phelelep/ProjetElecLORA_GSM/CompteRendu_Xavier/08_10_2025.md

# CR - MIRRIONE Xavier  
## Séance du 08/10/2025  
Schéma général projet
---

### Compréhension du projet

Le projet consiste à rendre **connectée une ruche**.Elle sera capable de collecter et transmettre des données à distance via GSM, soit SMS Téléphone.  
Deux principaux sytèmes sont utilisés :
- **LoRa** : module permettant l’envoi de données avec une **très faible consommation d’énergie**, mais un **débit limité**. Il sert à **récupérer les informations** provenant de toutes les ruches.  
- **GSM (SIM7000G)** : module de communication **longue portée**, utilisé pour **transmettre les données** LoRa vers un **téléphone** ou un **serveur en ligne**.

L’ensemble du circuit est alimenté par une **source d’énergie externe de 3.5 V**.

**Exemples de données collectées :**
- Température de la ruche  
- Poids de la ruche

Schéma général projet

---

### Prise en main du projet précédent

- La carte électronique fabriquée par l’équipe précédente ne sera pas réutilisée, car elle n’est pas fonctionnelle.  
- Nous allons utiliser une breadboard pour réaliser les connexions entre les modules à l’aide de fils.  
  → Cela permettra de tester et valider chaque module séparément avant d’intégrer le tout sur un PCB final.  
- Une partie du code LoRa de l’équipe précédente est disponible dans leur compte rendu.  
- Nous allons nous baser sur leur travail pour avancer plus rapidement et efficacement dans notre propre développement.
- Le code pour la partie GSM étais fonctionnel 

---

### Prochaines étapes du projet

1. **Prendre en main la partie LoRa**
   - Vérifier le **bon fonctionnement du module LoRa**.  
   - Reprendre et tester le **code source** fourni par l’équipe précédente.  
   - S’assurer que la communication **en émission et réception** fonctionne correctement.
2. **Prise en main du Module GSM**
    - arriver à envoeyr des messages avec une carte SIM
3. **Rélier Lora en utilisant l'ESP32 pour établier une communication avec le GSM**  
    - Integration LoRA & ESP32
    - Ajout du GSM

**Outils utilisés :**
- Logiciel : **Arduino IDE**  
- Code source : celui de l'ancienne l’équipe va être réutilisé et amélioré si nécessaire en fonction de nos besoins.

---
