phelelep/ProjetElecLORA_GSM/eco_conception/Project eco-conception.docx

# Projet Eco conception

GATEWAY LORA-GSM

# Étape 1 — Contexte environnemental et enjeux du numérique

Le secteur numérique représente aujourd’hui environ 4 à 5 % des émissions mondiales de gaz à effet de serre, avec un taux de croissance rapide. Au-delà du carbone, les équipements électroniques (EEE) posent des problèmes spécifiques à chaque phase de leur vie.

Fabrication : utilisation de matériaux rares (déplétion des ressources abiotiques), émissions GES importantes (ex. STMicroelectronics à Rousset : > 300 GWh/an), consommation d’eau (1,5 million de m³/an à Rousset).

Usage : principalement de l’énergie électrique, mais multiplié par le nombre très élevé d’appareils en service.

Fin de vie : génère des déchets électroniques (e-waste) fortement polluants. En 2022, 62 millions de tonnes de déchets électroniques produits dans le monde, dont seulement 22,3 % collectés et recyclés (Global E-waste Monitor 2022).

Pour les ingénieurs, l’écoconception représente un levier majeur : réduire la taille des puces, utiliser moins de matériaux rares dès la phase de design, prévoir le démontage et le recyclage.

# Étape 2 — Qu’est-ce que l’ACV ?

“ L’ACV est une méthode permettant de mesurer les impacts environnementaux d’un produit ou d’un service. ” — Pr. Luc Deneire, Polytech Nice Sophia Antipolis

Elle couvre l’intégralité du cycle de vie du produit : de l’extraction des matières premières jusqu’à la fin de vie, en passant par la fabrication, la distribution et l’usage.

## ACV Attributionnelle

Décrit tous les flux physiques pertinents qui contribuent et qui sont la conséquence d’un cycle de vie.

- Objectif principal 1 : identifier quels sous-systèmes (composants) ont le plus d’impact.
- Objectif principal 2 : identifier quelles phases du cycle de vie (fabrication, usage, fin de vie) ont le plus d’impact.
- Approche retenue pour ce projet.

## ACV Conséquentielle

Décrit quels flux environnementaux seront le plus impactés par des modifications de conception du produit.

- Objectif principal : déterminer quelle modification du produit a du sens sur le plan environnemental.
- Sera utilisée en phase d’interprétation pour formuler des recommandations.

# Étape 3 — Portées de l’ACV

Trois périmètres sont possibles selon la norme ISO 14040 :

Cradle to grave (Berceau à tombe) : périmètre le plus complet — de l’extraction des matières premières jusqu’à la fin de vie (recyclage ou mise en décharge). C’est le périmètre retenu pour ce projet.

Cradle to gate (Berceau à porte) : de l’extraction jusqu’à la sortie d’usine. Adapté quand la phase usage est negligeable ou inconnue.

Gate to gate (Porte à porte) : uniquement la phase de fabrication. Utile pour comparer deux procédés de production.

Choix pour ce projet : Cradle to grave — nous intégrons la fabrication, 5 ans d’usage (électricité de recharge) et la fin de vie (collecte DEEE).

# Étape 4 — Définition et objectifs de l’ACV

## Objectifs

Cette ACV attributionnelle a pour but d’évaluer l’empreinte environnementale de la passerelle LoRa-GSM conçue dans le cadre du projet ruche connectée. Elle est réalisée dans un contexte académique (cours d’écoconception, Polytech, Université Côte d’Azur). Le produit étudié est un prototype.

## Unité fonctionnelle (UF)

Selon le cours (slide 30), l’unité fonctionnelle doit suivre le format : verbe d’action + niveau de performance quantifié + conditions d’utilisation.

“ Assurer la collecte locale (via LoRa) et la transmission distante (via GSM/LTE) des paramètres environnementaux d’une ruche, à une fréquence d’un envoi toutes les heures, dans un environnement rural extérieur (IP65), pour une durée de vie anticipée de 5 ans. ”

Questions soulevées par la durée de vie (analogie avec l’exemple du convertisseur Buck du cours) :

- La durée de vie réelle de la batterie LiPo est-elle de 5 ans ? Un remplacement anticipé (2–3 ans) multiplierait l’impact de ce composant.
- Où fonctionne la gateway ? En France, le mix électrique est bas-carbone (0,057 kg CO₂eq/kWh). Dans un pays au mix charbon, l’impact de la phase usage serait nettement plus élevé.
- Le mode Deep Sleep de l’ESP32 et du module LoRa est activement utilisé, ce qui réduit significativement la consommation en phase usage.

## Champ de l’étude (Scope)

Périmètre : Cradle to grave — extraction des matières premières → fabrication → usage 5 ans → fin de vie.

## Flot de référence

Quantité du produit nécessaire pour atteindre l’unité fonctionnelle : 1 unité de passerelle LoRa-GSM (masse totale ≈ 276 g, hors énergie).

## Frontières du système

Inclus : extraction des matières premières, fabrication des composants électroniques (ESP32, SIM7000G, LLCC68, PCB, passifs), assemblage, phase d’usage 5 ans (électricité de recharge batterie : 87,6 kWh), fin de vie DEEE.

Exclus : phase R&D, transport entre usines, infrastructure serveur de réception des données, maintenance et remplacement de composants hors batterie.

Localisation : usage en France — mix électrique français, source Electricity Maps.

Période : 5 ans de fonctionnement.

# Étape 5 — Inventaire — Bill of Materials (BOM)

Pour l’électronique, l’inventaire du cycle de vie repose principalement sur le BOM (Bill of Materials), comme indiqué en slide 33 du cours. Le tableau ci-dessous liste l’ensemble des composants de la passerelle LoRa-GSM avec leur correspondance dans la base de données EcoInvent, tels qu’ils ont été introduits dans le logiciel OpenLCA.

Bloc / Module | Désignation | Nom EcoInvent | Cat. | Qté | Masse/Surface | Unité
ESP32 WROOM | Circuit imprimé (PCB) | printed wiring board, SMT, Pb-free | PCB | 1 | 0,0072 m² | m²
ESP32 WROOM | Montage CMS PCB | mounting, SMT, Pb-free solder | PCB | 1 | 0,0072 m² | m²
ESP32 WROOM | Microcontrôleur ESP32 (QFN-40) | wafer, fabricated, for IC | IC | 1 | 25 mm² | mm²
ESP32 WROOM | Mémoire Flash SPI (SOIC-8) | integrated circuit, logic type | IC | 1 | 1,08 g | g
ESP32 WROOM | Oscillateur Quartz | integrated circuit, logic type | IC | 1 | 0,6 g | g
ESP32 WROOM | Condensateurs de découplage (0402) | capacitor, for SMT | Passif | 15 | 0,37 g/pèce | g
ESP32 WROOM | Résistances pull-up/down (0402) | resistor, surface-mounted | Passif | 10 | 0,10 g/pèce | g
SIM7000G | Circuit imprimé (PCB) | printed wiring board, SMT, Pb-free | PCB | 1 | 0,0072 m² | m²
SIM7000G | Montage CMS PCB | mounting, SMT, Pb-free solder | PCB | 1 | 0,0072 m² | m²
SIM7000G | Modem cellulaire (TFBGA-361) | wafer, fabricated, for IC | IC | 1 | 144 mm² | mm²
SIM7000G | Connecteurs antenne U.FL/SMA | electric connector, PCI buss | Périph. | 2 | 0,57 g/pèce | g
SIM7000G | Condensateurs tantale (1206) | capacitor, tantalum, through-hole | Passif | 4 | 0,016 g/pèce | g
SIM7000G | Support carte SIM | electric connector, peripheral | Périph. | 1 | 1,00 g | g
SIM7000G | Diodes de protection ESD (SOT-23) | integrated circuit, logic type | IC | 2 | 0,017 g/pèce | g
SIM7000G | Régulateur LDO (transistor SMD) | transistor, surface-mounted | Passif | 1 | 0,06 g | g
SIM7000G | Self DC/DC (inductance 1008) | inductor, low value multilayer chip | Passif | 1 | 0,112 g | g
LoRa LLCC68 | Circuit imprimé (PCB) | printed wiring board, SMT, Pb-free | PCB | 1 | 0,0072 m² | m²
LoRa LLCC68 | Montage CMS PCB | mounting, SMT, Pb-free solder | PCB | 1 | 0,0072 m² | m²
LoRa LLCC68 | Transceiver LoRa LLCC68 (QFN-24) | wafer, fabricated, for IC | IC | 1 | 16 mm² | mm²
LoRa LLCC68 | Oscillateur Quartz | integrated circuit, logic type | IC | 1 | 0,6 g | g
LoRa LLCC68 | Pin headers de connexion | electric connector, PCI buss | Périph. | 8 | 0,71 g/pèce | g
LoRa LLCC68 | Inductances RF d’adaptation (0402) | inductor, low value multilayer chip | Passif | 4 | 0,001 g/pèce | g
Cartes | Connecteur USB-C alimentation | electric connector, peripheral | Périph. | 1 | 2,25 g | g
Cartes | Boutons poussoir Reset/Boot | switch, toggle type | Passif | 2 | 4,00 g/pèce | g
Cartes | LEDs d’indicateur d’état (0603) | diode, glass, for SMT | Passif | 3 | 0,08 g/pèce | g
Cartes | Résistances pour LEDs (0603) | resistor, surface-mounted | Passif | 3 | 0,042 g/pèce | g
Batterie | Batterie Lithium-ion | battery, Li-ion — EcoInvent | Batterie | 1 | 20 g | g
Boîtier | Boîtier ABS IP65 | ABS plastic — EcoInvent | Boîtier | 1 | 150 g | g
Antennes | Antennes GSM + LoRa | — | — | 1 | 30 g | g
Énergie | Électricité usage (5 ans, France) | electricity, low voltage, FR | Énergie | 1 | 87,6 kWh | kWh
TOTAL | 30 références composants + énergie | | | | ≈ 276 g + 87,6 kWh

Le détail complet des correspondances EcoInvent est disponible dans le fichier composants_ecoinvent.xlsx joint au dépôt GitHub.

# Creation du processus et du flow

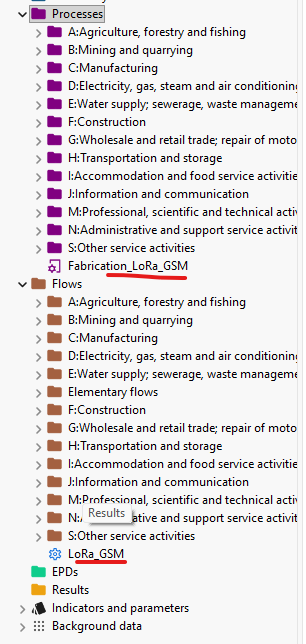
[picture p59: figure]

# Creation des inputs

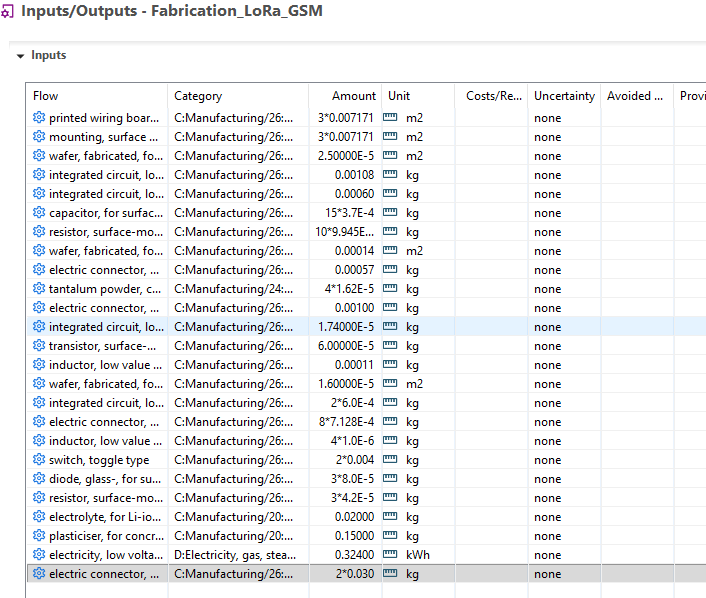
[picture p60: figure]

Les inputs dans le processus “Fabrication_ LoRa_GSM”

Chaquet donne du tableau Excel et été introduite

# Création du Product System

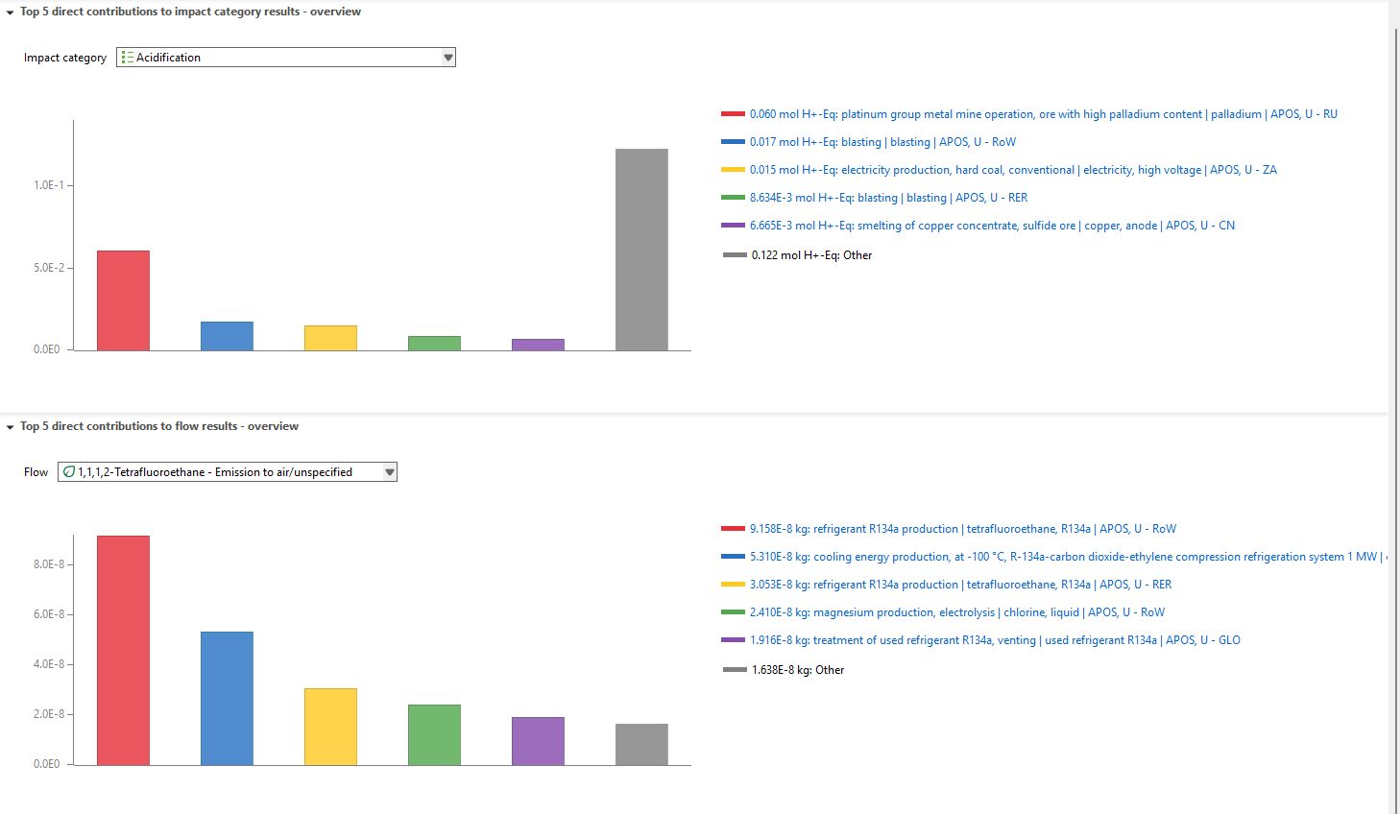
[picture p61: figure]
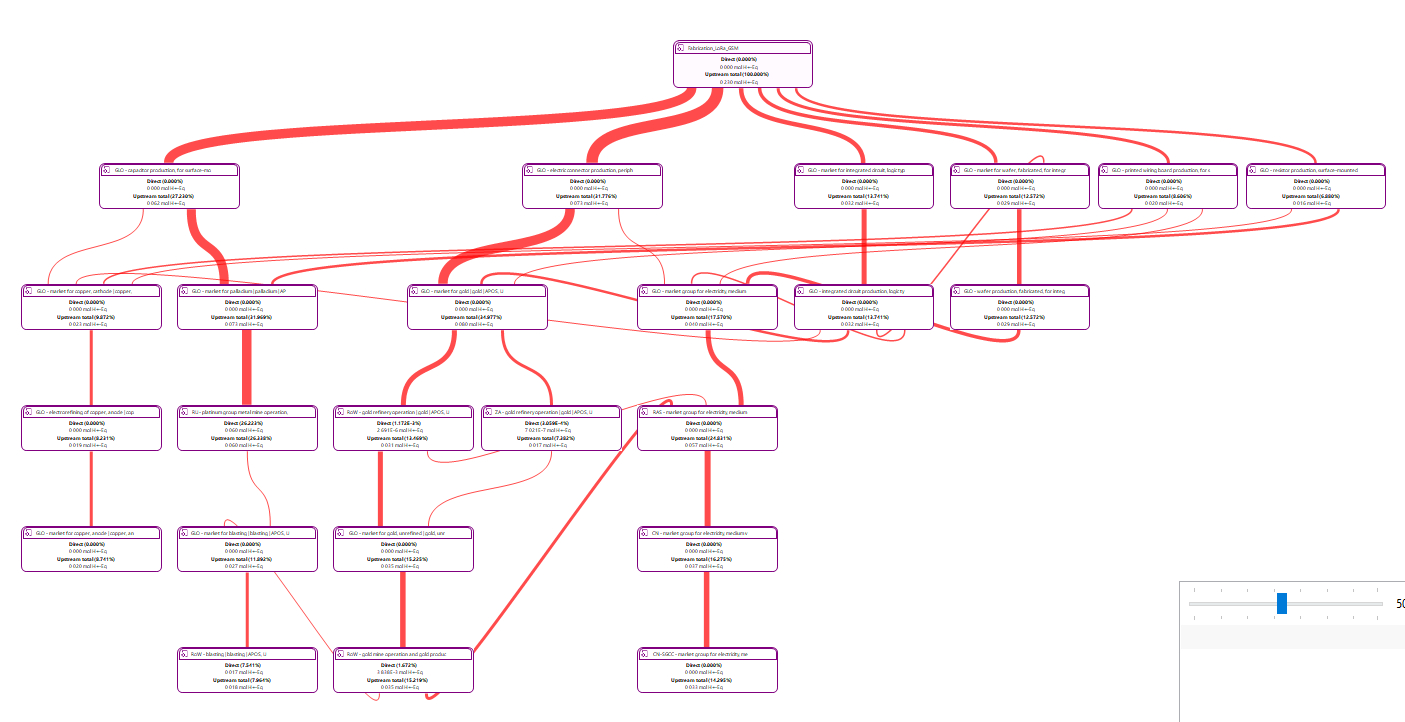
[picture p62: figure]

- On remarque que la fabrication La fabrication = 80-90% de l'impact
- L'usage (10-20% de l'impact) : Grâce à au LoRa et du Deep Sleep, la part de l'électricité sera très faible.

# Étape 7 — Analyse Opex vs Capex : fabrication vs usage

L’un des enseignements majeurs du cours (slides 17–18, illustré sur le smartphone) est le rapport entre l’impact à la fabrication (Capex) et l’impact à l’usage (Opex).

Capex (fabrication) : 80 à 90 % de l’impact total pour les équipements électroniques. Inclut l’extraction des matériaux rares, la production des semi-conducteurs et l’assemblage des cartes.

Opex (usage) : 10 à 20 % de l’impact. Principalement lié à la consommation électrique de recharge de la batterie.

Pour notre gateway, ce ratio est particulièrement favorable à la phase usage grâce aux deux optimisations logicielles clés implémentées dans le projet :

- Mode Deep Sleep de l’ESP32 : consommation descendant à quelques µA lors des périodes d’inactivité.
- Protocole LoRa : radio longue portée à très faible puissance (quelques mW en émission), contrairement au WiFi ou au Bluetooth classique.

La consommation estimée sur 5 ans est d’environ 87,6 kWh, soit environ 1,5 à 2 mAh par heure en moyenne. Avec le mix électrique français (0,057 kg CO₂eq/kWh), cela représente environ 5 kg CO₂eq sur 5 ans pour la seule phase usage, soit une fraction minoritaire du bilan total.

# L’analyse de l’impact de notre projet

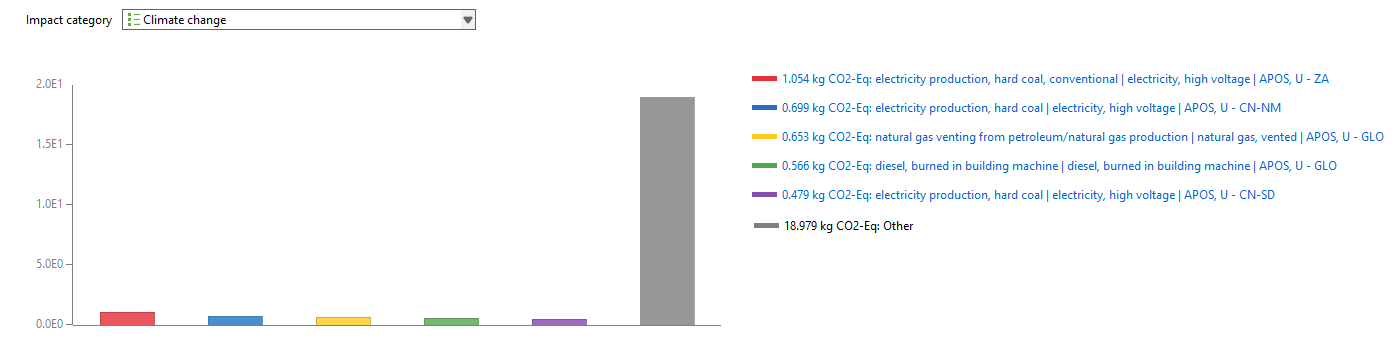
[picture p63: figure]

Notre Gateway de ruche émet environ 20 5 kg de CO2 sur l'ensemble de son cycle de vie (fabrication + 5 ans d'usage). Pour te donner une idée, c'est l'équivalent d'environ 100 à 120 km parcourus par une voiture thermique moyenne. Pour un objet électronique complexe (GSM + LoRa + Batterie), c'est un score très correct.

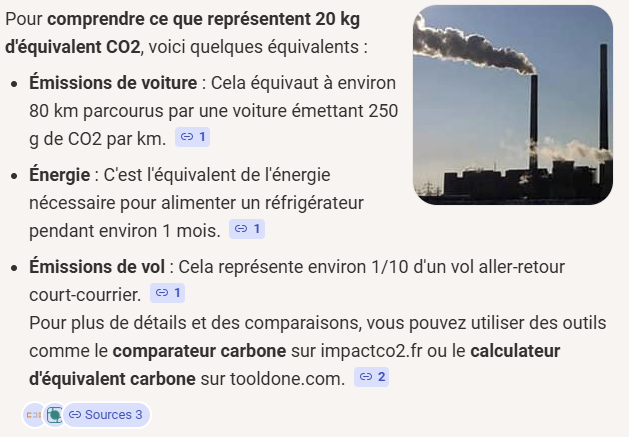
[picture p64: figure]

Source google.com

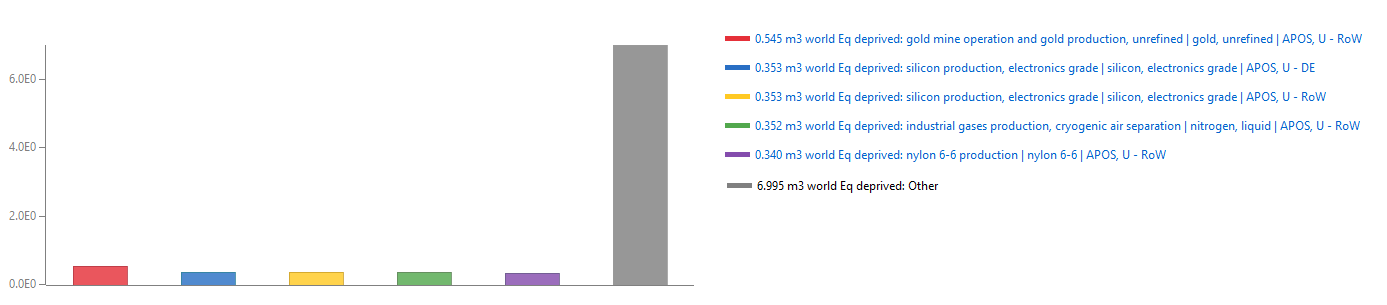
[picture p65: figure]

8m³ d'eau environ pour notre projet ce qui reste corect si le projet reste fonctionnel pendant 5 ans. Et condition qu’il ne nécessite pas une intervention humaine durant les 5 années.

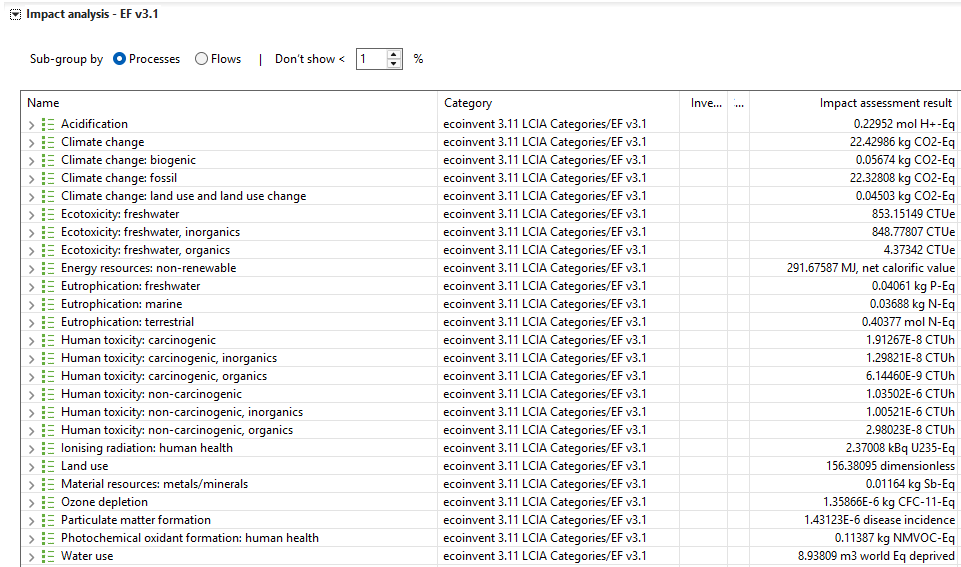
[picture p66: figure]

- Mineral resource scarcity : Ce chiffre représente l'épuisement des métaux (Or, Cuivre, Lithium). C'est souvent l'impact le plus fort de l'électronique.
- Terrestrial ecotoxicity : les ruches sont dans la nature. Cela mesure l'impact potentiel des composants si le boîtier se dégrade ou est mal recyclé.

# Étape 6 — Évaluation des impacts

## Les 16 catégories d’impact (méthode ReCiPe / CML)

La méthode ACV normalisée définit jusqu’à 16 catégories d’impact. Les résultats sont exprimés en unités communes (impacts mid-point), puis peuvent être agrégés en impacts end-point sur la santé, les écosystèmes et les ressources.

# | Catégorie d’impact | Unité | Priorité | Pertinence pour l’électronique

1 | Climate change | kg CO₂ eq | ★★★ | Principale — émissions GES de la fabrication et de l’usage
2 | Mineral resource scarcity | kg Cu eq | ★★★ | Principale — métaux rares : or, cuivre, lithium, cobalt
3 | Water consumption | m³ eq | ★★★ | Principale — semi-conducteurs très consommateurs en eau
4 | Terrestrial ecotoxicity | kg 1,4-DCB | ★★★ | Principale — dégradation boîtier ou mauvais recyclage DEEE
5 | Human toxicity (cancer) | kg 1,4-DCB | ★★★ | Principale — traitement des semi-conducteurs
6 | Ozone depletion | kg CFC-11 eq | ★
7 | Ionizing radiation | kBq Co-60 eq | ★
8 | Photochemical ozone formation | kg NMVOCs | ★★
9 | Particulate matter formation | kg PM₂,5 eq | ★★
10 | Terrestrial acidification | kg SO₂ eq | ★★
11 | Freshwater eutrophication | kg P eq | ★
12 | Marine eutrophication | kg N eq | ★
13 | Freshwater ecotoxicity | kg 1,4-DCB | ★★
14 | Marine ecotoxicity | kg 1,4-DCB | ★★
15 | Land use | m² annum crop eq | ★
16 | Fossil resource scarcity | kg oil eq | ★★

Légende : ★★★ = catégorie principale pour l’électronique (mise en évidence en jaune), ★★ = catégorie secondaire, ★ = faible pertinence pour ce type de produit.

## Résultats obtenus sur OpenLCA pour notre passerelle

# L’analyse de la contribution

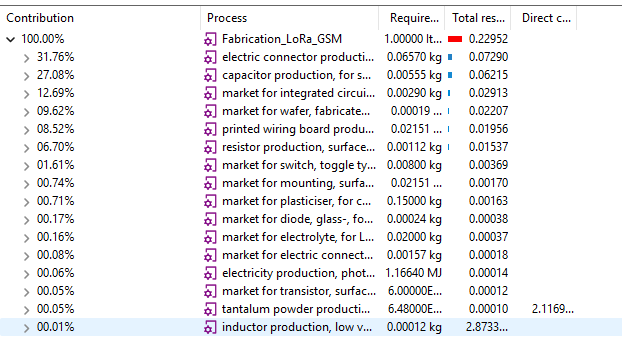
[picture p67: figure]

D'après le graphique c’est l'extraction des matériaux et la fabrication des composants complexes (puces, PCB) qui pèsent le plus.

# Étape 8 — Interprétation des résultats

## Principaux enseignements de l’ACV

Les résultats obtenus dans OpenLCA confirment le schéma classique de l’électronique : la fabrication représente 80–90 % de l’impact total. Ce ratio est identique à celui du smartphone présenté en cours (slides 22–24).

Climate change (≈ 20,5 kg CO₂eq) : Équivalent à 100–120 km en voiture thermique. Pour un objet combinant GSM + LoRa + batterie, c’est un bilan très correct.

Water consumption (≈ 8 m³) : Essentiellement lié à la fabrication des semi-conducteurs (silicium, cuivre). Acceptable sur 5 ans sans intervention.

Mineral resource scarcity : L’impact le plus élevé proportionnellement — extraction d’or, cuivre, lithium, cobalt. Surtout dô à la batterie LiPo et aux PCB multicouches.

Terrestrial ecotoxicity : Indicateur à surveiller car les ruches sont en milieu naturel. L’impact survient si le boîtier se dégrade ou si le produit est mal recyclé (DEEE).

L’analyse de contribution confirme que les composants complexes (puces électroniques, PCB multicouches) et l’extraction des métaux constituent les “points chauds” prioritaires sur lesquels concentrer les efforts d’amélioration.

## Recommandations d’écoconception (ACV conséquentielle)

Sur la base de l’ACV attributionnelle, les pistes d’amélioration suivantes sont identifiées (approche conséquentielle, slide 21) :

1. Prolonger la durée de vie : Passer de 5 à 10 ans diviserait l’impact fabrication par deux sur l’unité fonctionnelle. Cela implique de choisir des composants à MTBF élevé et de prévoir des mises à jour logicielles (firmware OTA).

2. Réduire la capacité de la batterie : Le Deep Sleep permet d’évaluer si une batterie plus petite (1 000 mAh) suffit, réduisant l’impact du lithium et du cobalt.

3. Faciliter le démontage et le recyclage : Utiliser des vis plutôt que de la colle, marquer clairement les plastiques (ABS), prévoir la séparabilité batterie/PCB pour le tri DEEE.

4. Optimiser le PCB : Un PCB 2 couches au lieu de 4 réduit la quantité de cuivre et de résine époxy ; envisager un PCB sans halogène (halogen-free) pour limiter l’écotoxicité.

5. Localisation de la fabrication : Assembler en Europe avec de l’électricité renouvelable réduit les émissions de fabrication.

# Étape 9 — Comparaison avec l’exemple du cours (convertisseur Buck)

Le professeur utilise en cours (slides 37–38) un convertisseur Buck disponible sur GitHub comme exemple pratique d’ACV. La comparaison avec notre gateway est instructive :

Unité fonctionnelle du Buck (cours) : “ Assurer la régulation d’une tension continue (abaissement de 12 V à 5 V) pour une charge de 5 W pendant 15 000 heures de fonctionnement. ”

Unité fonctionnelle de notre gateway : “ Assurer la collecte et la transmission des données environnementales d’une ruche via LoRa et GSM/LTE, pendant 5 ans de fonctionnement extérieur. ”

Les mêmes questions que le prof pose pour le Buck s’appliquent à notre projet :

- La batterie est-elle bien dimensionnée pour 5 ans ? Si la durée de vie réelle est de 2–3 ans, l’impact de ce composant doit être multiplié.
- Le circuit est-il bien dimensionné pour la charge réelle ? Le mode Deep Sleep réduit fortement la consommation effective.
- Où fonctionne le circuit ? Le mix électrique français est favorable (nucléaire + renouvelables = 0,057 kg CO₂eq/kWh vs > 0,4 en Pologne ou Allemagne).

# Étape 10 — Vocabulaire OpenLCA

Après démarrage d’OpenLCA et chargement de la base EcoInvent, les concepts clés utilisés dans ce projet sont les suivants :

Process : Le processus de fabrication ou d’usage. Dans notre cas : “ Fabrication_LoRa_GSM ” (regroup e tous les composants du BOM) et “ Usage_LoRa_GSM ” (87,6 kWh d’électricité sur 5 ans).

Flow : Les flux entrants (inputs : matériaux, énergie) et sortants (outputs : produit fini, déchets). Chaque ligne du BOM correspond à un flow entrant dans le processus de fabrication.

Product System : L’assemblage de tous les processus liés au cycle de vie. Il connecte fabrication, usage et fin de vie en un seul système à évaluer.

Impact Assessment : Le calcul des indicateurs environnementaux à partir des flux physiques. OpenLCA utilise les données EcoInvent pour convertir les masses de composants en kg CO₂eq, m³ d’eau, etc.

Reference Flow : La quantité de référence du produit à évaluer. Ici : 1 unité de gateway LoRa-GSM.

Annexe :

## Sources utilises :

Composant | Information à extraire | Source
ESP32 WROOM | Consommation | ESP32 Wi-Fi & Bluetooth Modules I Espressif (https://www.espressif.com/en/products/modules/esp32)
SIM7000G | Courant de transmission LTE | https://www.simcom.com/product/SIM7000G.html - Recherche Google (https://www.google.com/search?q=https://www.simcom.com/product/SIM7000G.html)
Poids des CMS | Masse des résistances/condos | mouser.fr
Boitier ABS | Masse et Volume plastique | https://www.hammondmfg.com/scpg.htm - Recherche Google (https://www.google.com/search?q=https://www.hammondmfg.com/scpg.htm)
Facteurs d'impact | Emissions CO2 des matériaux | Base Empreinte® (https://base-empreinte.ademe.fr/)
Mix Électrique | Impact du kWh par pays | Carte | Electricity Maps (https://app.electricitymaps.com/map/live/fifteen_minutes)

CEBAN Daniel & MIRRIONE Xavier

Éco conception 2025-2026 CEBAN Daniel & MIRRIONE Xavier _________________________________________________________________________________
