phelelep/ProjetElecLORA_GSM/Presentation finale projetLoRa-GSM.pdf

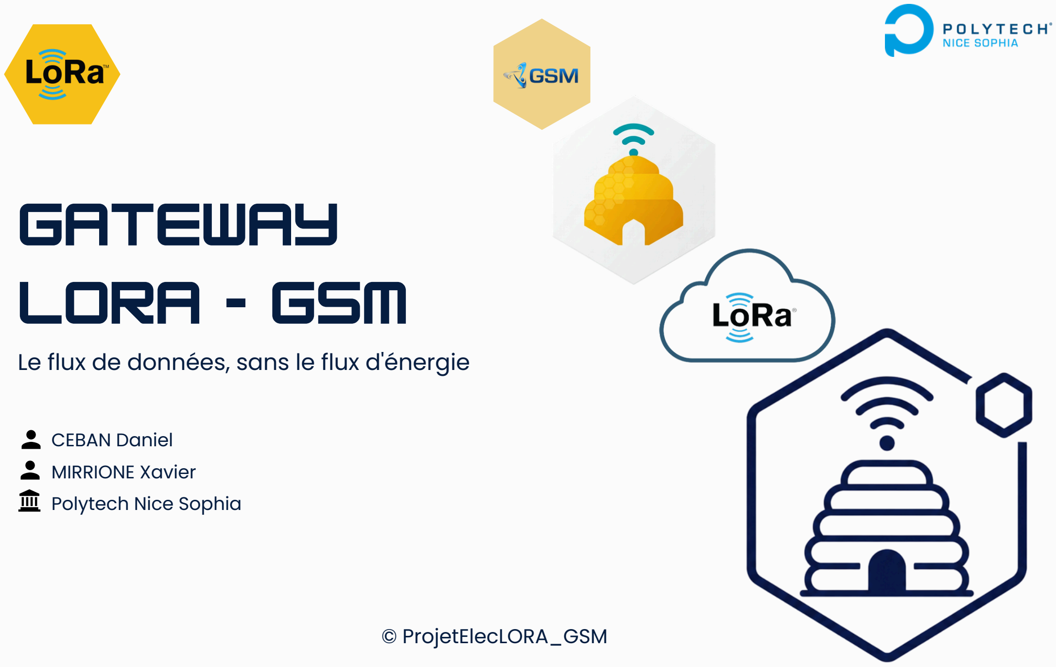
[picture p68: page 1]

Le flux de données, sans le flux d'énergie

# GATEWAY LORA - GSM

© ProjetElecLORA_GSM

CEBAN Daniel
MIRRIONE Xavier
Polytech Nice Sophia

# SOMMAIRE

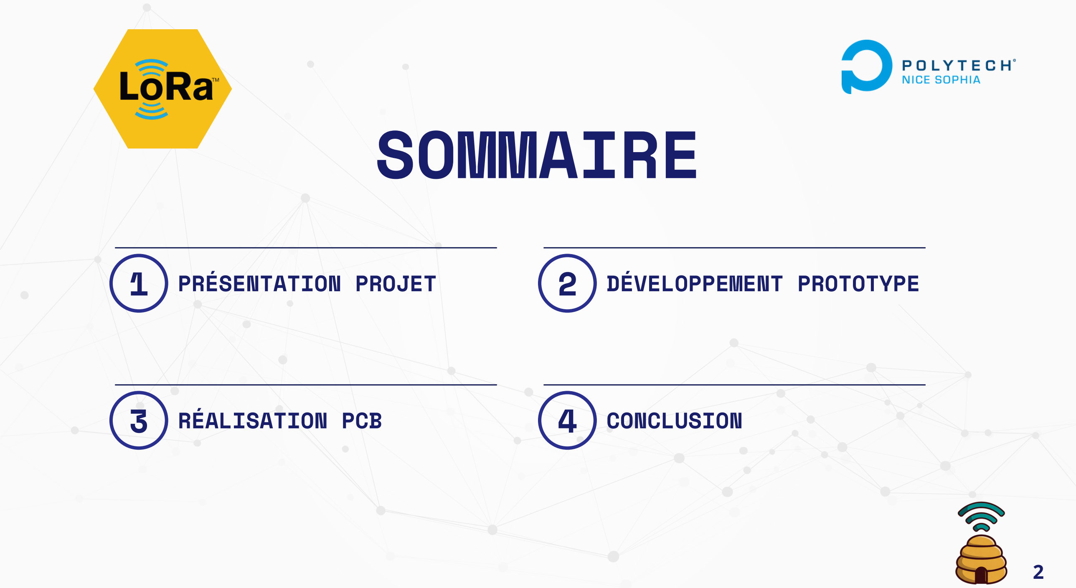
[picture p69: page 2]

1 PRÉSENTATION PROJET | 2 DÉVELOPPEMENT PROTOTYPE
3 RÉALISATION PCB | 4 CONCLUSION

2

# PRÉSENTATION PROJET

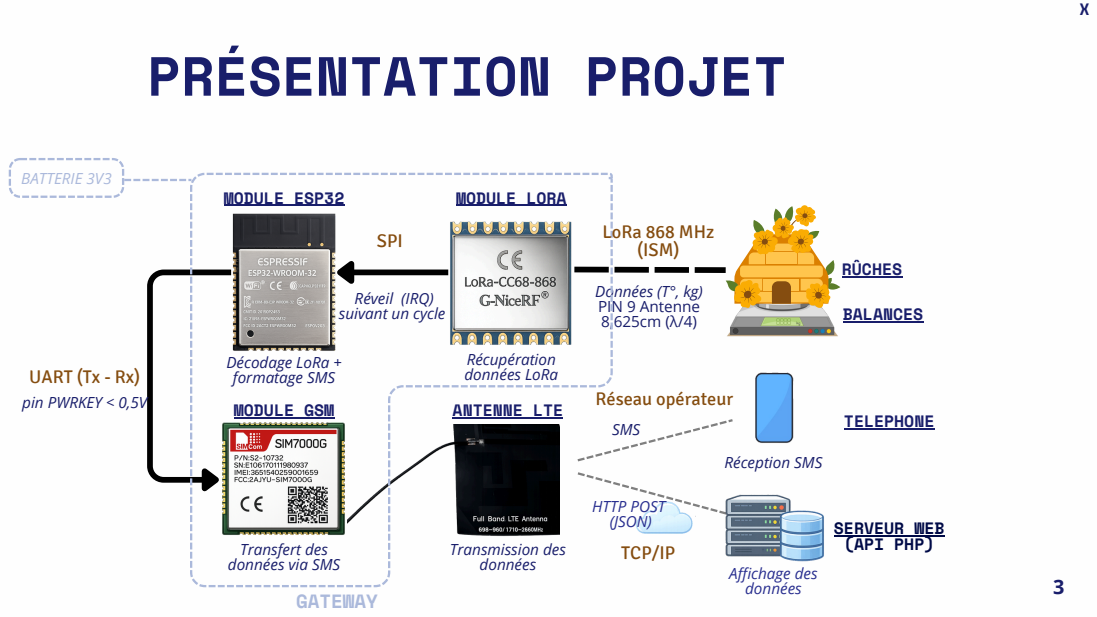
[picture p70: page 3]
Décodage LoRa + formatage SMS; Données (T°; , kg) PIN 9 Antenne 8,625cm (λ/4); SPI; Récupération données LoRa; MODULE ESP32; MODULE LORA; MODULE GSM; Transmission des données; ANTENNE LTE; Réseau opérateur; SMS; BATTERIE 3V3; Réception SMS; TELEPHONE; RÛCHES; BALANCES; LoRa 868 MHz (ISM); SERVEUR WEB (API PHP); Affichage des données; TCP/IP; HTTP POST (JSON)

Réveil (IRQ)
suivant un cycle

UART (Tx - Rx)
pin PWRKEY < 0,5V

Transfert des
données via SMS
GATEWAY

## AGENCEMENT DU TRAVAIL D’ÉQUIPE

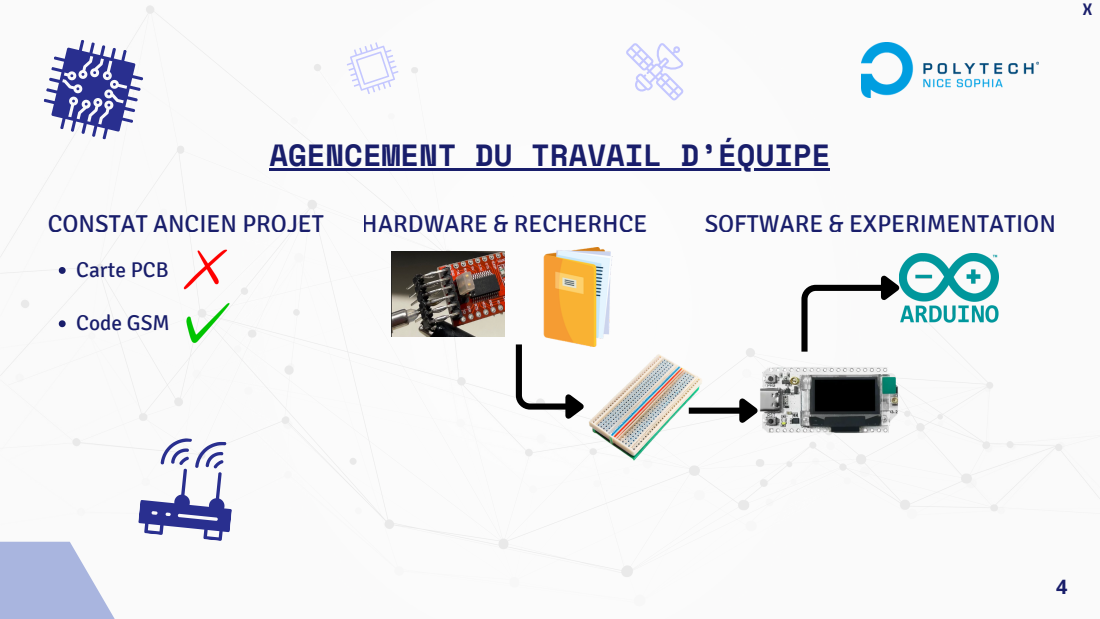
[picture p71: page 4]
CONSTAT ANCIEN PROJET; HARDWARE & RECHERHCE; SOFTWARE & EXPERIMENTATION; Carte PCB; Code GSM

# Développement prototype

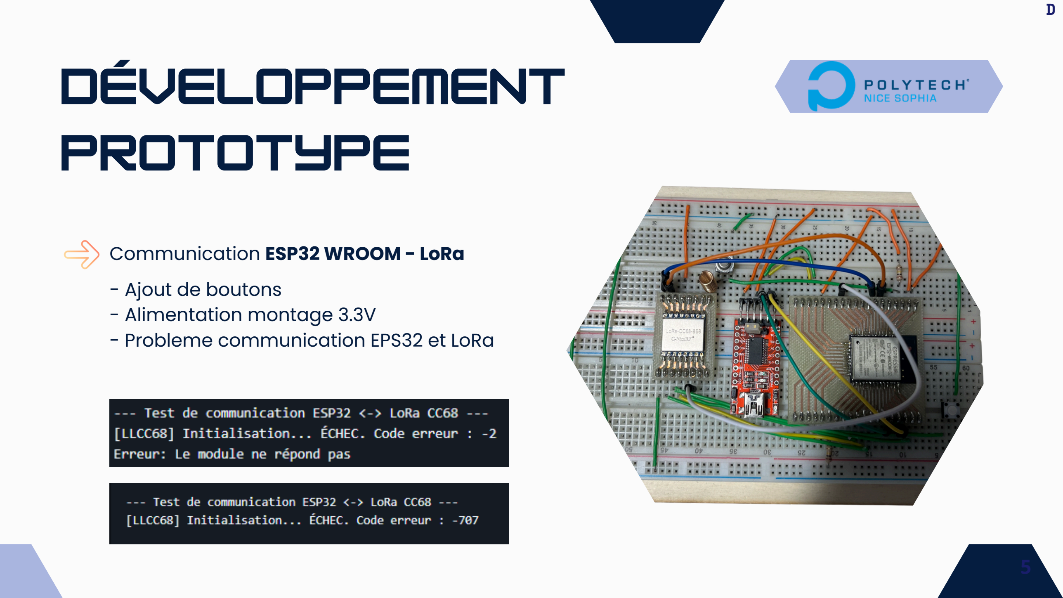
[picture p72: page 5]

5

Communication ESP32 WROOM - LoRa
- Ajout de boutons
- Alimentation montage 3.3V
- Probleme communication EPS32 et LoRa

D

# Développement prototype

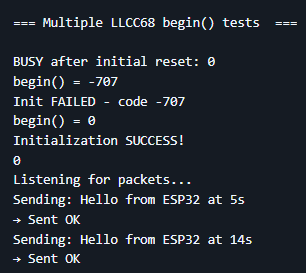
[picture p73: figure]

- Tests avec la bibliothèque “LoRa.h” et “RadioLib.h”

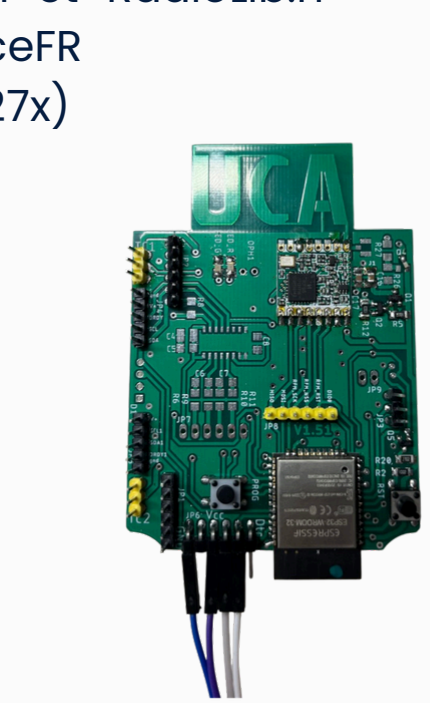
[picture p74: figure]

- Tests avec LoRa-CC68-868 G-NiceFR
- Test avec module RF96 (type SX127x)
- Tests en boucle

RÉSOLUTION PROBLÈME COMMUNICATION

6

# Développement prototype

7

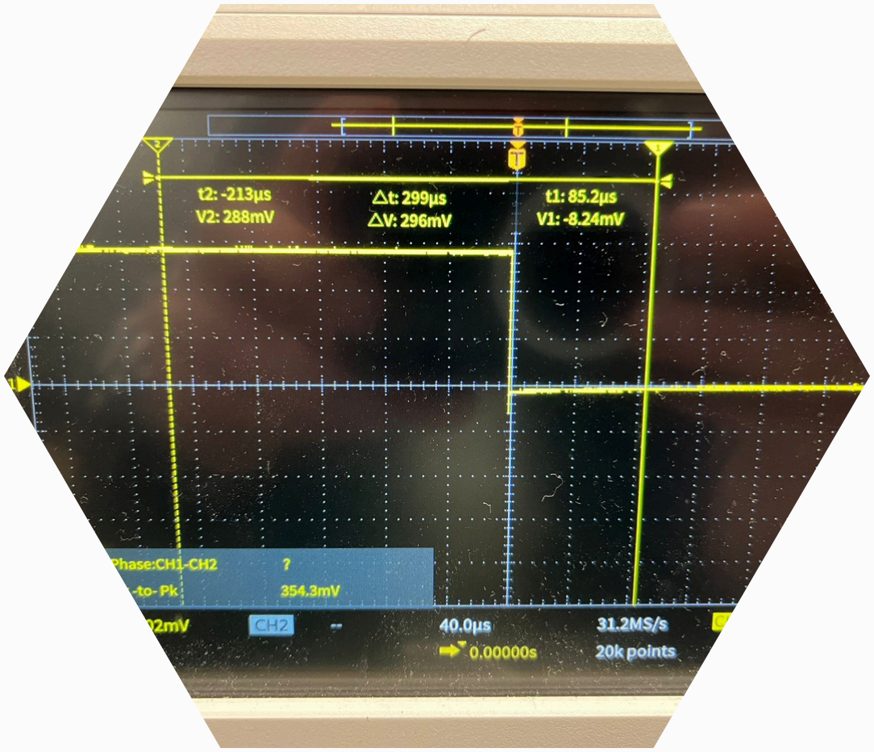
[picture p75: figure]

Réveil de l’ESP32 par LoRa
-LoRa : écouté en permanence -LoRa : Impulsion sur le pin DIO1 si message reçu
-ESP32 : réveil si impulsion du pin DIO1 -ESP32 : réinitialiser le DIO1 à “LOW” -ESP32 : réceptionner et traitement du message
-ESP32 : endormissement après 10 secondes d’inactivité

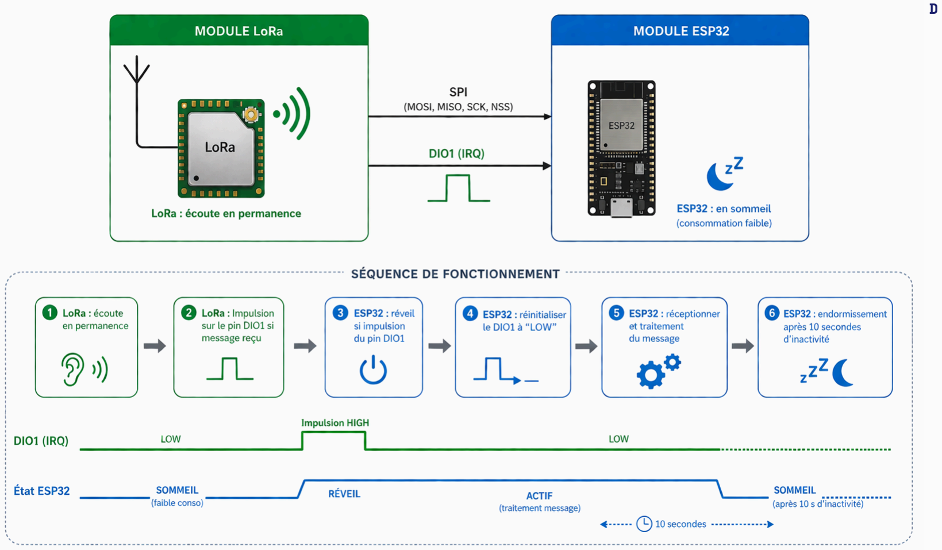
[picture p76: page 8]

# Développement prototype

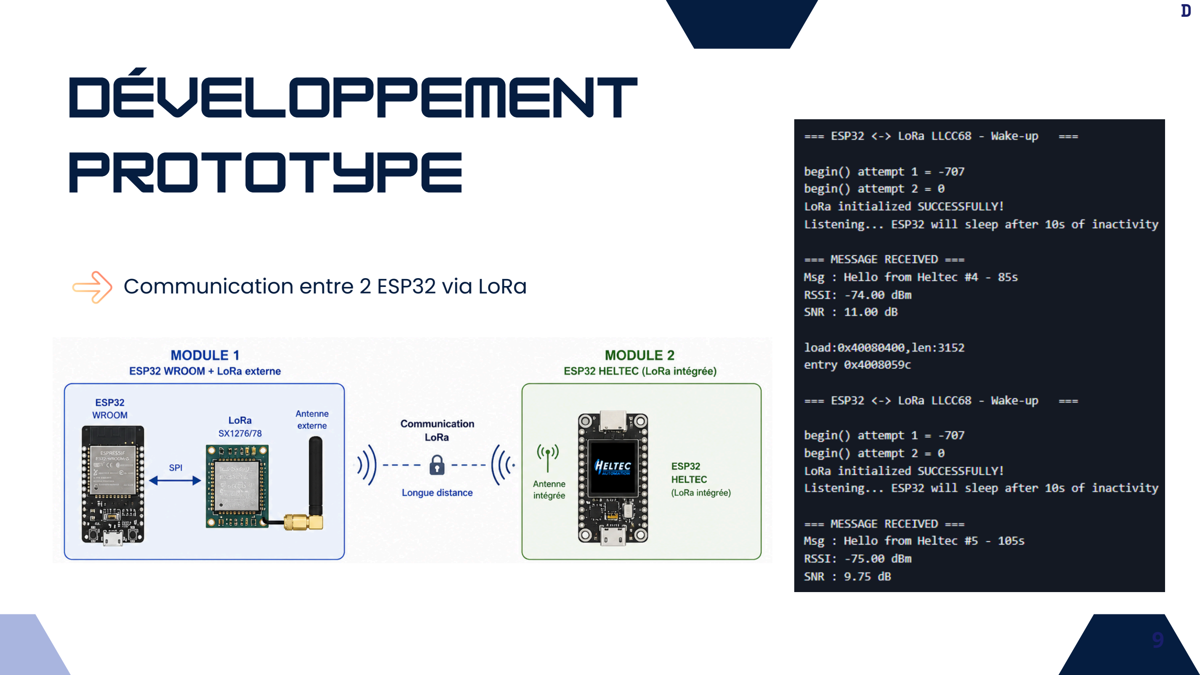
[picture p77: page 9]

9

Communication entre 2 ESP32 via LoRa

# Développement prototype

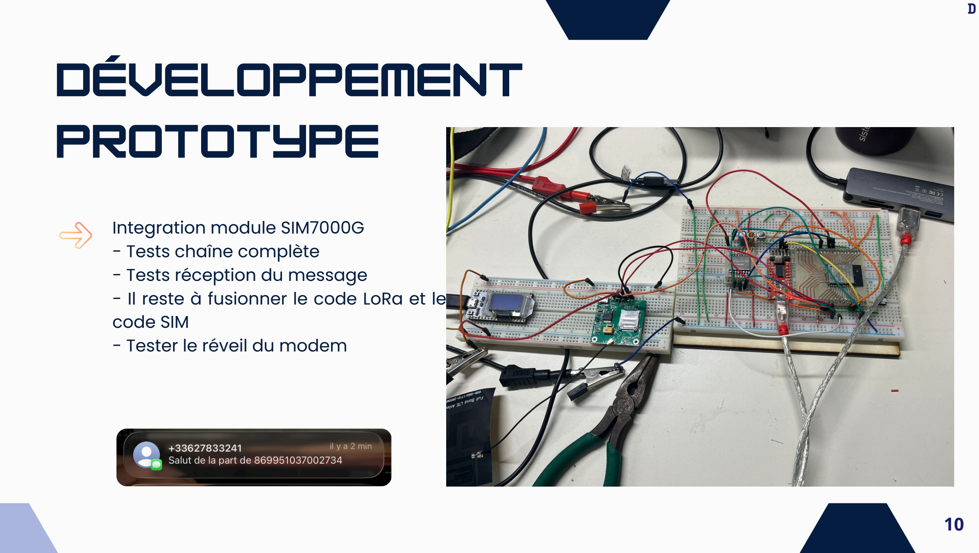
[picture p78: page 10]

10

Integration module SIM7000G
- Tests chaîne complète
- Tests réception du message
- Il reste à fusionner le code LoRa et le code SIM
- Tester le réveil du modem

# Réalisation PCB

11

X

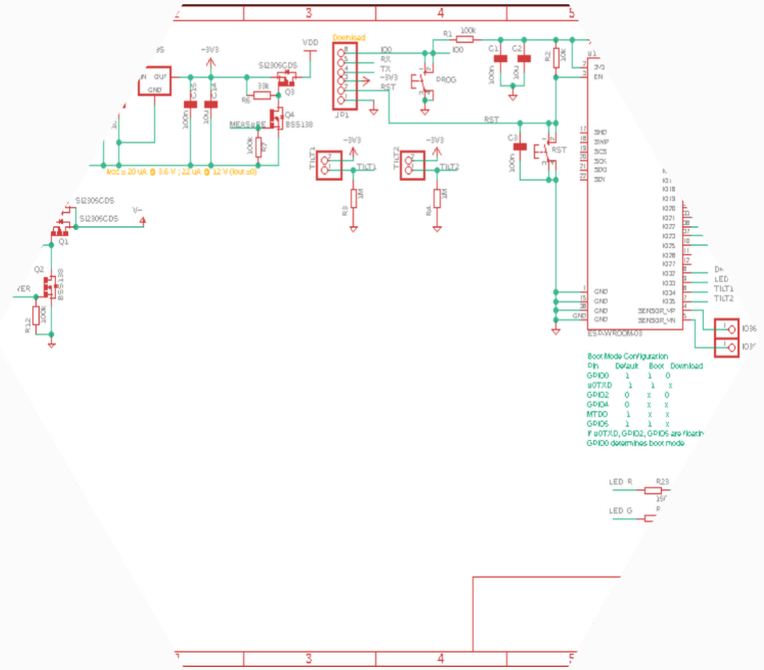
[picture p79: figure]

Réfléchir fonctionnellement, sans contraintes physiques Étapes clés de la réalisation :
1. Choix des composants et connexions (datasheets)
2. Composants passifs : condensateurs & résistances
3. Boutons RST & PROG pour la programmation
4. Circuit commande alimentation
Point de départ : version de l'

ancien groupe (ESP32 +
LoRa intégré)

# Réalisation PCB

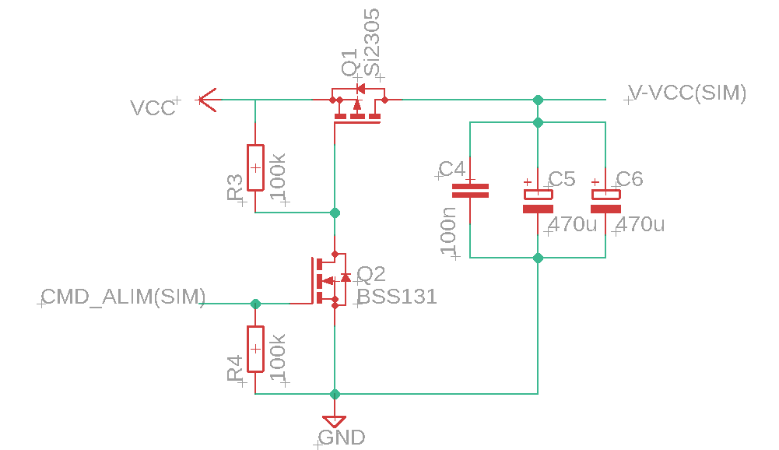
[picture p80: figure]

12

X

Problème : SIM7000G en mode sleep = 1,2 mA
Exigence prof : courant = 0 quand le module est inutilisé
Solution : coupure hardware via 2 transistors MOSFET
NMOS : BSS 131 & PMOS : SI2305 Contrôle : GPIO ESP32 (CMD_ALIM) coupe complètement l'

alimentation
SIM7000G

# Réalisation PCB

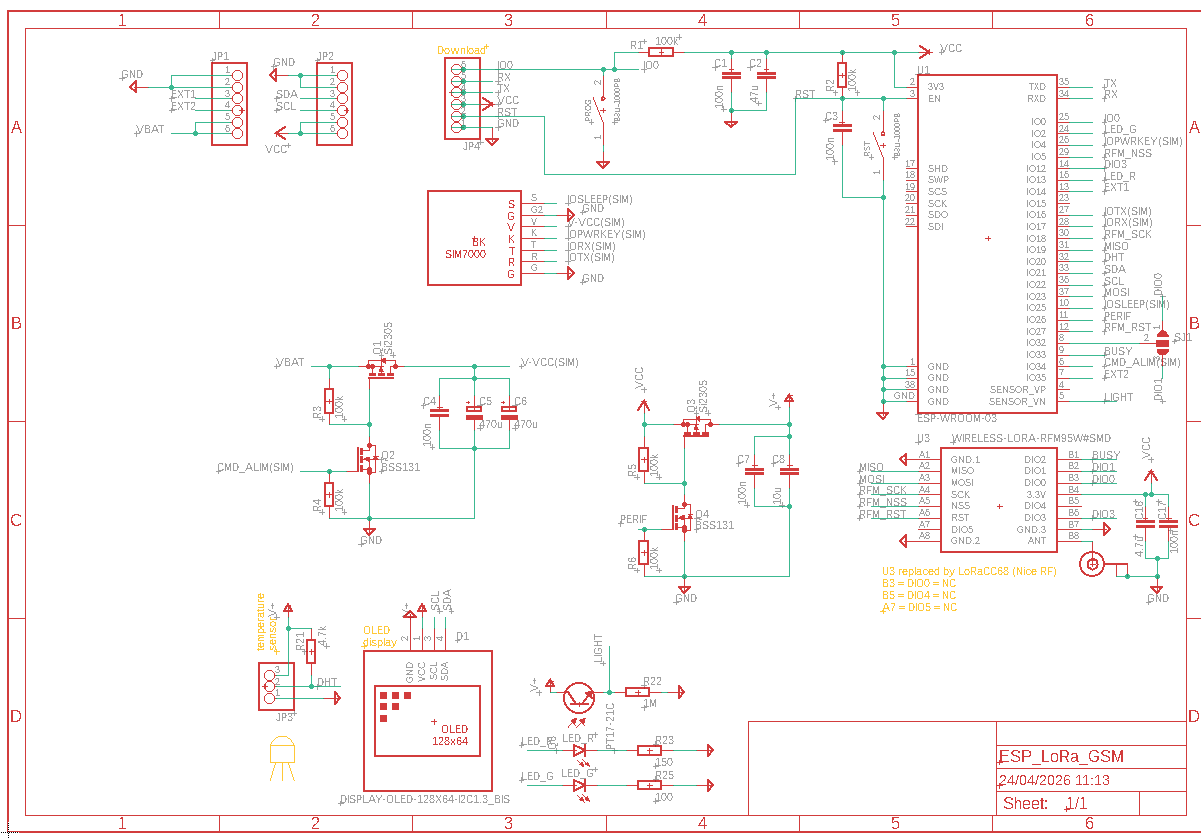
[picture p81: figure]

13

X

# Réalisation PCB

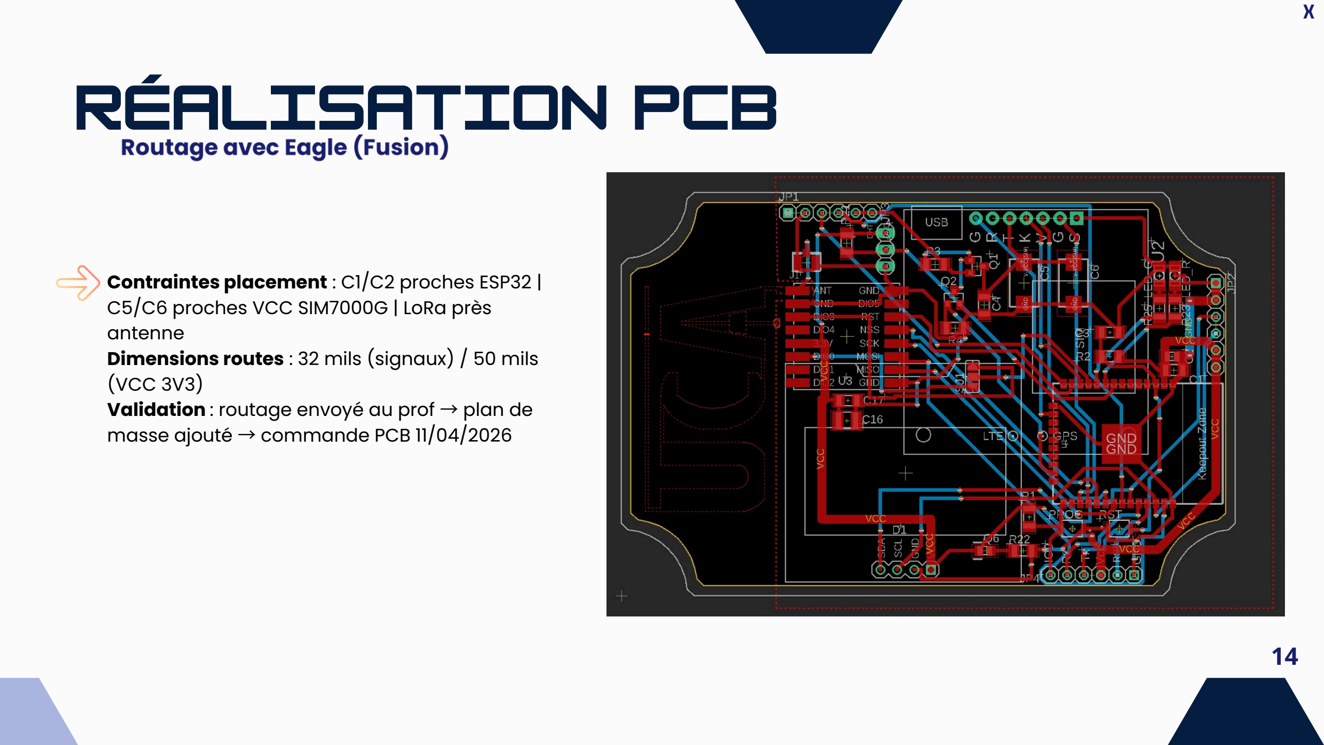
[picture p82: page 14]

14

X

Contraintes placement : C1/C2 proches ESP32 |
C5/C6 proches VCC SIM7000G | LoRa près
antenne
Dimensions routes : 32 mils (signaux) / 50 mils (VCC 3V3)
Validation : routage envoyé au prof → plan de masse ajouté → commande PCB 11/04/2026

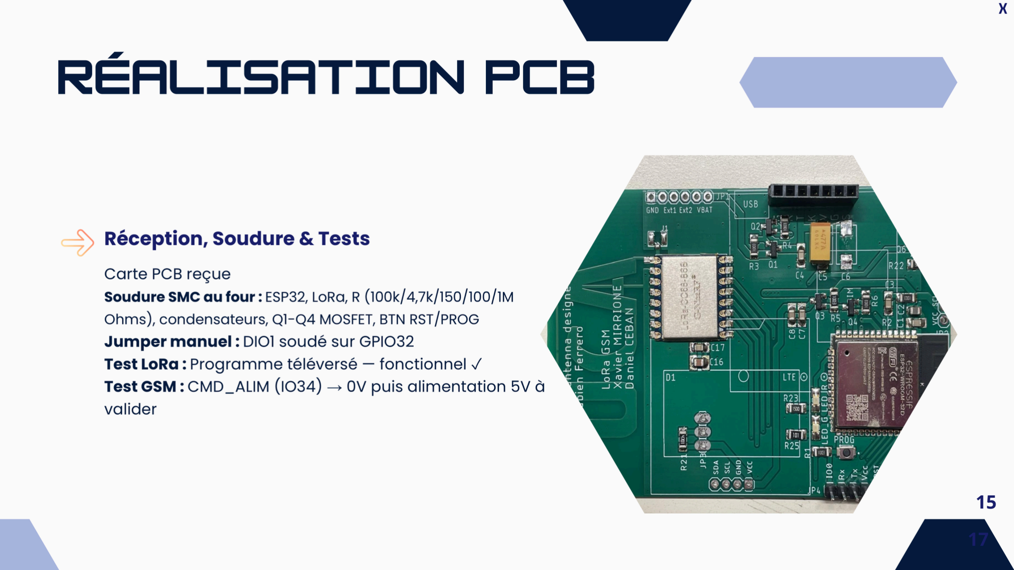
[picture p83: page 15]

15

# Conclusion

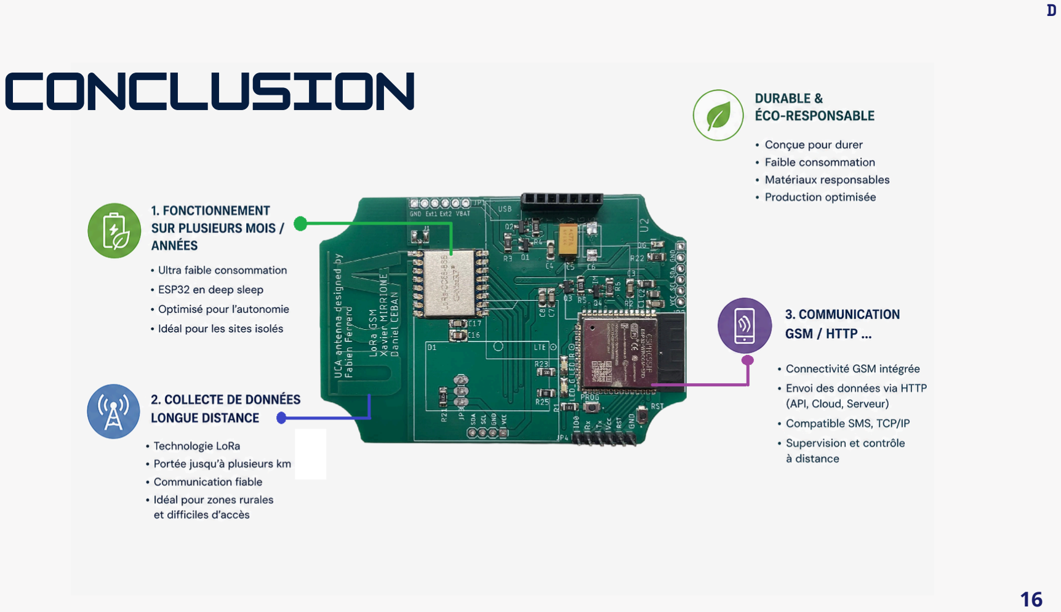
[picture p84: page 16]

16

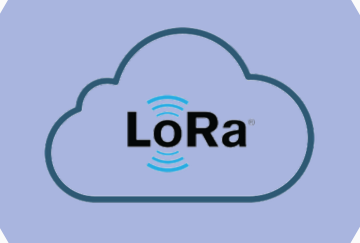
[picture p85: figure]

# MERCI!

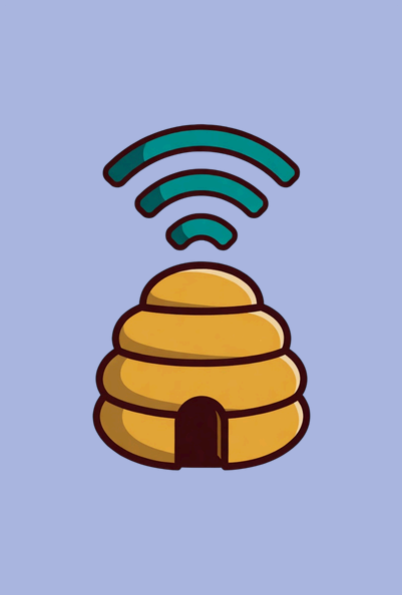
[picture p86: figure]

Des questions ?!

17

CEBAN Daniel
MIRRIONE Xavier
Polytech Nice Sophia

© ProjetElecLORA_GSM
