phelelep/ProjetElecLORA_GSM/CahierDesCharges.md

# Gateway LORA-GSM 

PROMOTION : ELSE4 FISA 2025-2026
- CEBAN Daniel
- MIRRIONE Xavier

## Définitions:

**LoRa** = Communication en longe distance et faible consommation énergetique.
**GSM (Global System for Mobile Communications) : *** = GSM est une norme de téléphonie mobile largement utilisée pour la communication cellulaire. Elle permet la transmission de voix et de données sur des réseaux mobiles à l’échelle mondiale, facilitant la connectivité mobile entre les appareils et les utilisateurs.

## 🎯 Objectif principal du projet

- Récupérer les données des ruches via le module **LoRa**, une technologie longue portée et à faible consommation, adaptée aux environnements isolés.  
- Concevoir une passerelle LoRa ↔ GSM permettant de transférer les données collectées depuis les ruches vers un réseau mobile.  
- Transmettre les informations à distance au client final grâce au module **GSM (SIM7000G)**, assurant une connectivité même sans réseau Wi-Fi.  
- Assurer la fiabilité et la faible consommation énergétique du système pour un fonctionnement autonome sur batterie.

## 🎯 Liste des objectifs

1. Utiliser le code fournit par l'quipe precedente pour etablier une communication avec le GSM.
     le module ESP32 (qui integre Lora) le connecter à SIM7000G, afin de d'envoier un signal à distance.
2. Implementer la partir LoRa pour recuperer un tramme des donnes.
3. Recevoir et traiter les données (témpérature, poids des ruches) transmises avec LoRa.
