phelelep/ProjetElecLORA_GSM/CompteRendu_Xavier/Seance9_21_01_2026.md

# CR - MIRRIONE Xavier  
## Séance 9 du 21/01/2026  

## CONTEXTE
L'après-midi suite à l'oral, quelques modifications doivent avoir lieu sur le schéma du projet. 
### Modification
Il manquait la partie HTTP avec la serveur swep où seront directement affiché les données.
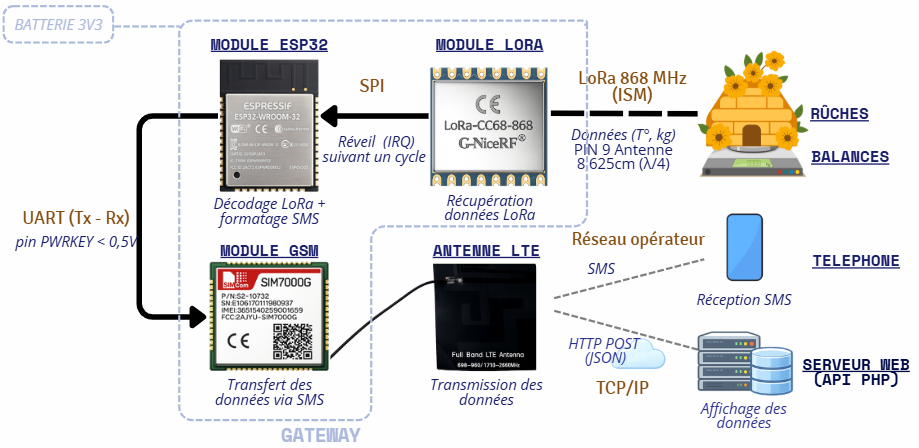
[picture p88: Images/SchemaGeneral3.png]
Schéma général projet
