phelelep/ProjetElecLORA_GSM/Images/Condensateur_C5-C6.jpeg

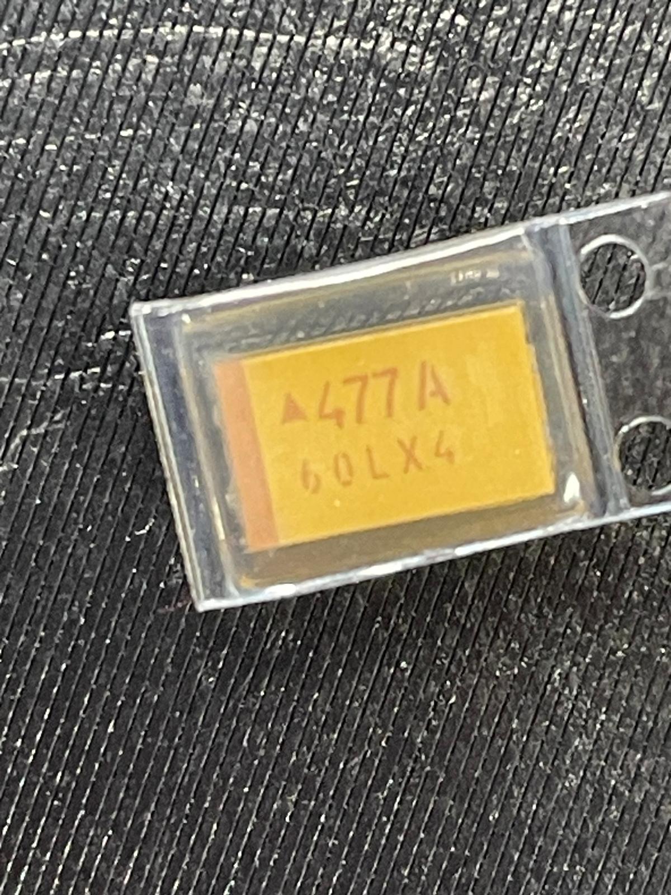
Images/Condensateur_C5-C6.jpeg
