phelelep/ProjetElecLORA_GSM/Images/ESP32-nue.jpg

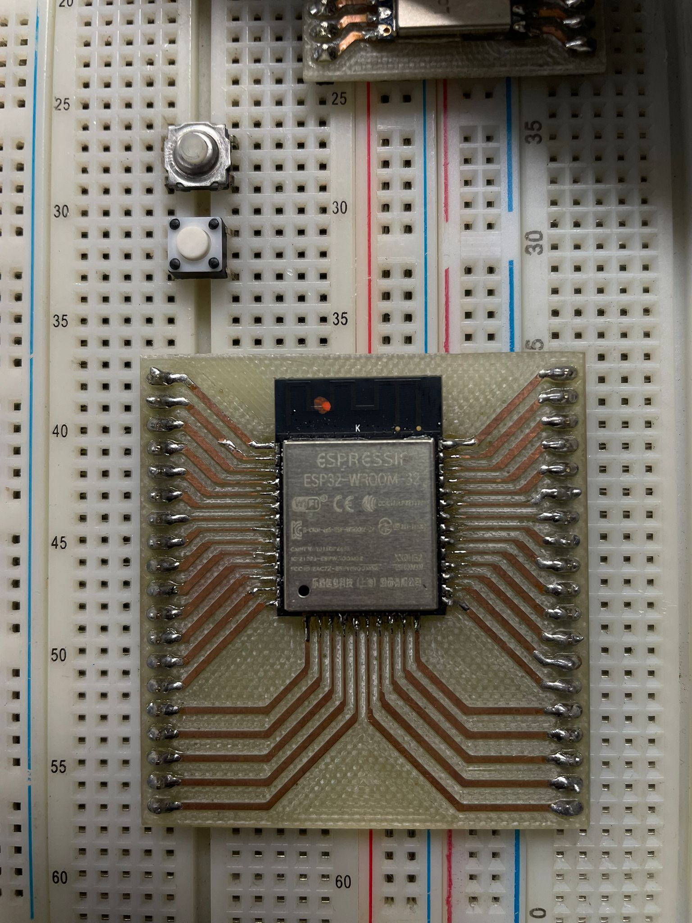
Images/ESP32-nue.jpg
