phelelep/ProjetElecLORA_GSM/Images/ESP32.png

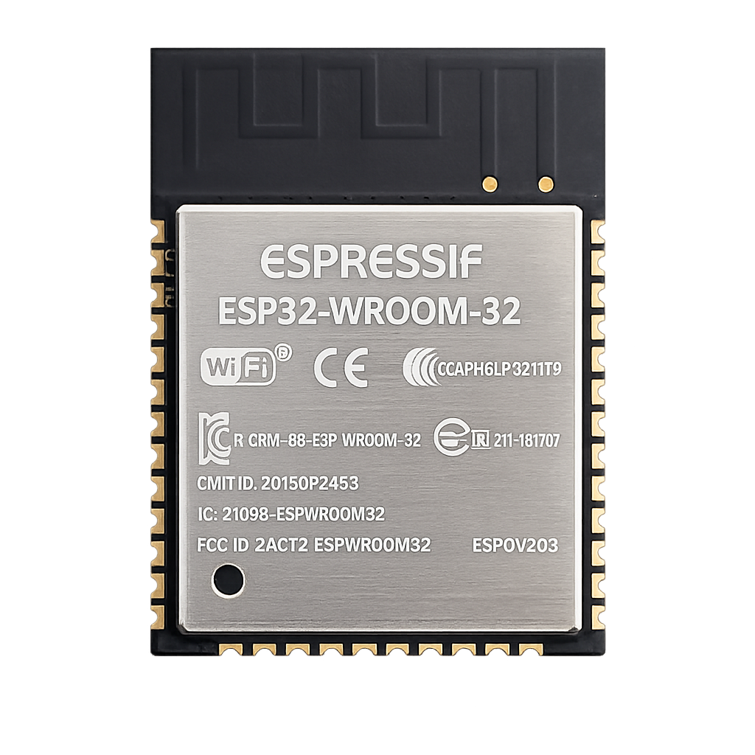
Images/ESP32.png
