phelelep/ProjetElecLORA_GSM/Images/GSM_PIN.jpg

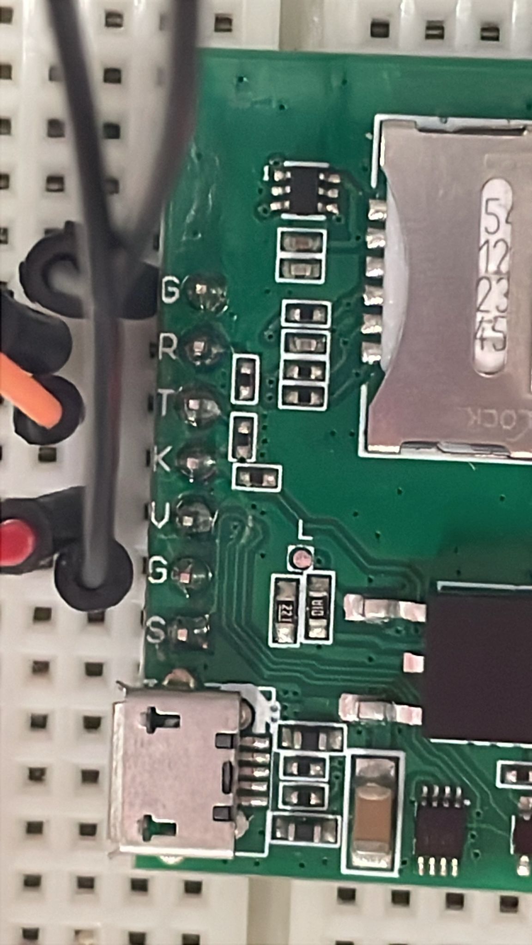
Images/GSM_PIN.jpg
