phelelep/ProjetElecLORA_GSM/Images/LoRa.png

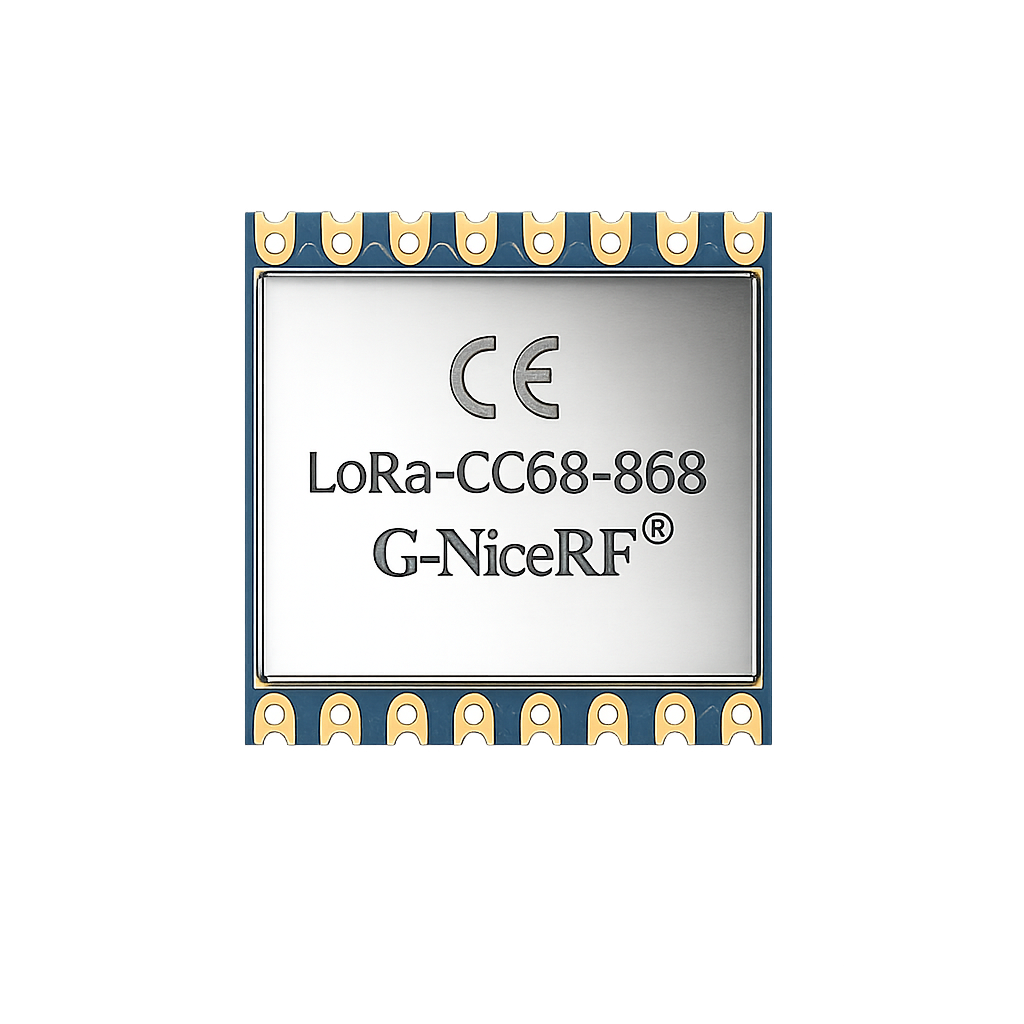
Images/LoRa.png
