phelelep/ProjetElecLORA_GSM/Images/PCB_Card_Composants_Sim7000.jpeg

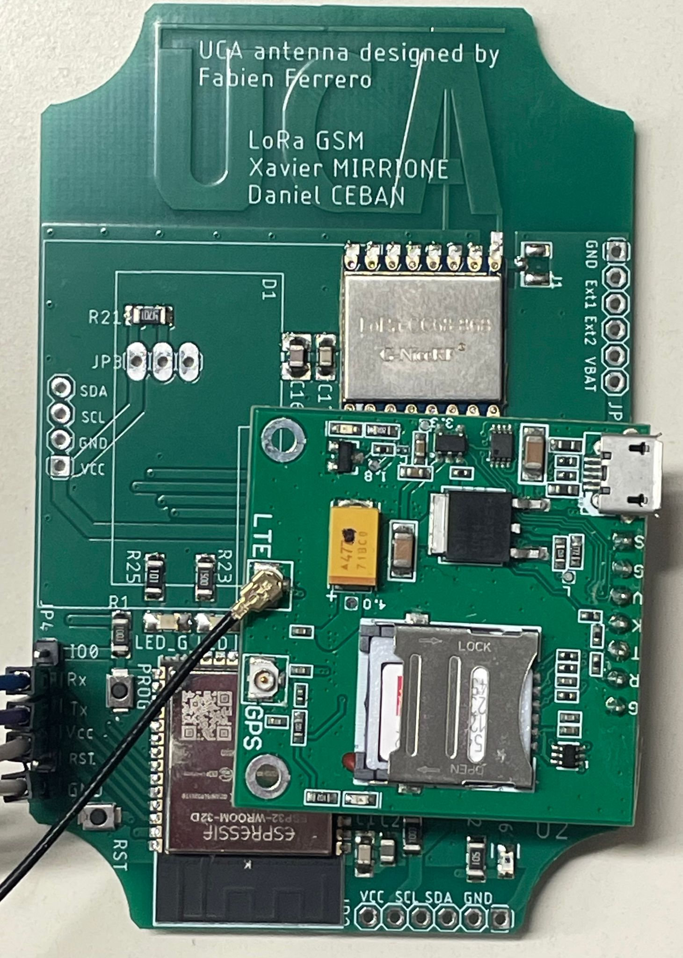
Images/PCB_Card_Composants_Sim7000.jpeg
