phelelep/ProjetElecLORA_GSM/Images/PCB_Card_nue.jpeg

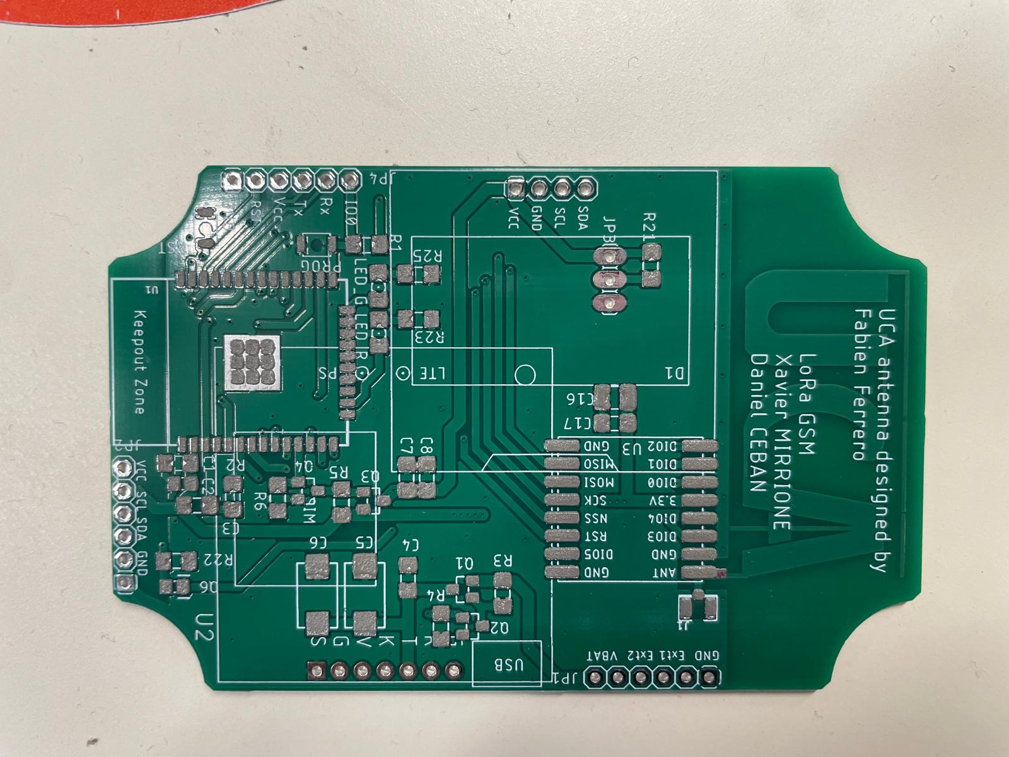
Images/PCB_Card_nue.jpeg
