phelelep/ProjetElecLORA_GSM/Images/photo_cablage-ESP32.jpeg

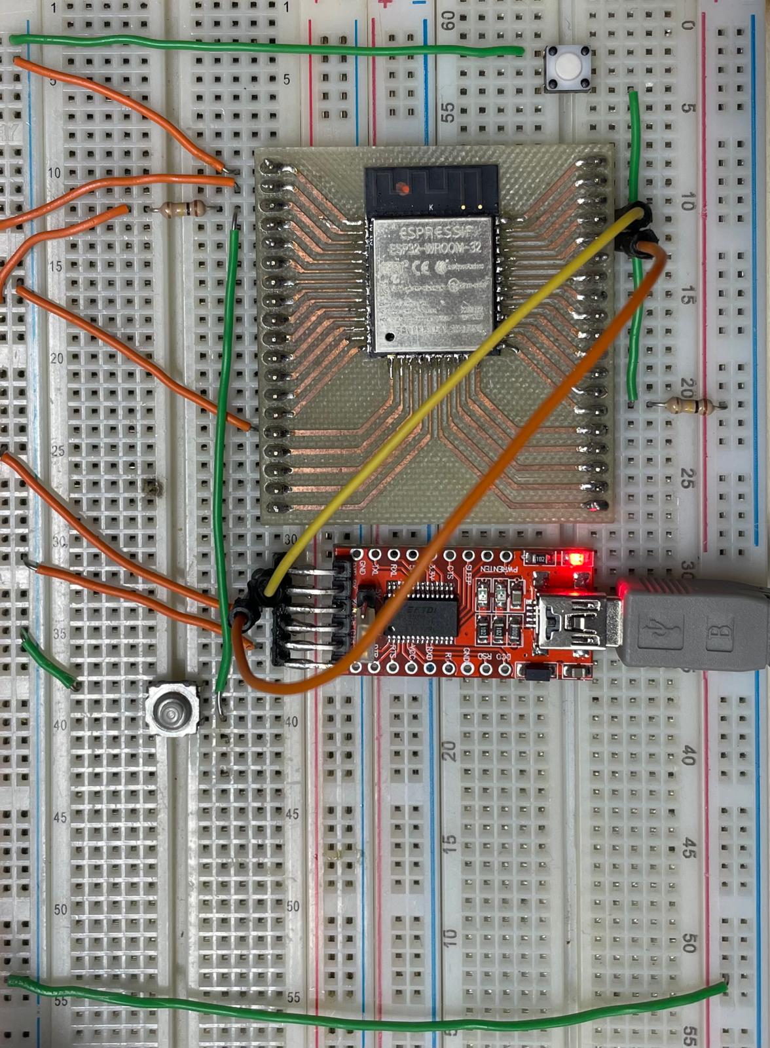
Images/photo_cablage-ESP32.jpeg
