phelelep/ProjetElecLORA_GSM/Images/Pin_Table.jpeg

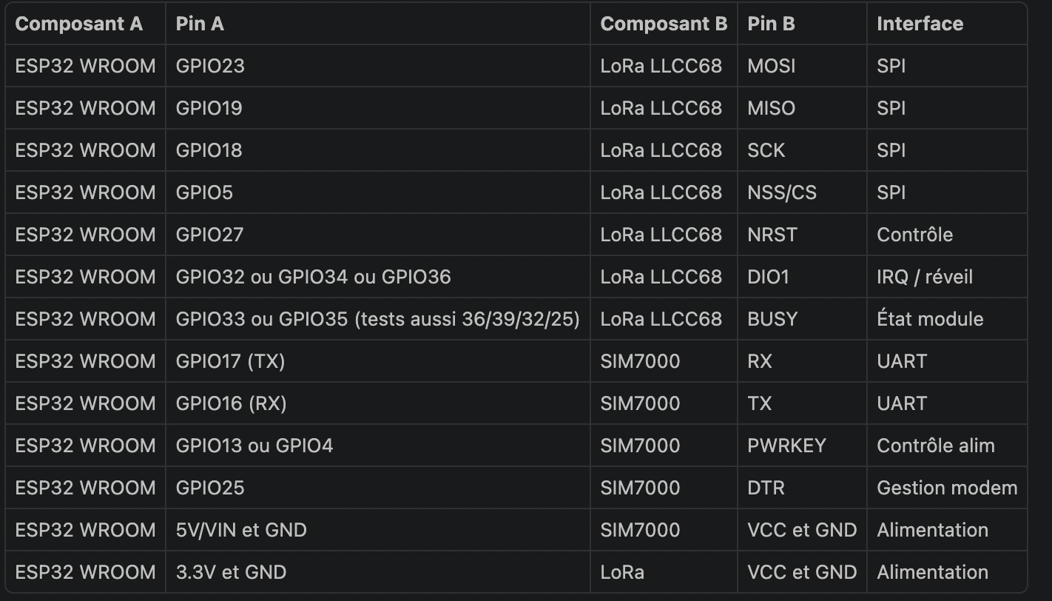
Images/Pin_Table.jpeg
