phelelep/ProjetElecLORA_GSM/Images/ServeurWeb.png

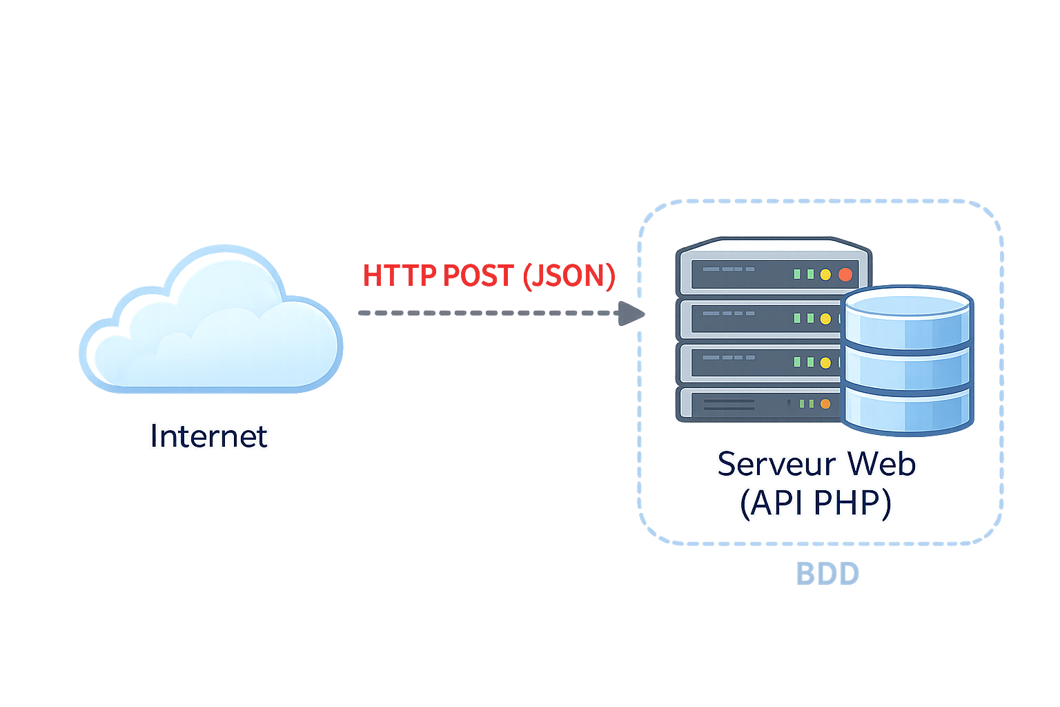
Images/ServeurWeb.png
