phelelep/ProjetElecLORA_GSM/Images/SIM7000G.png

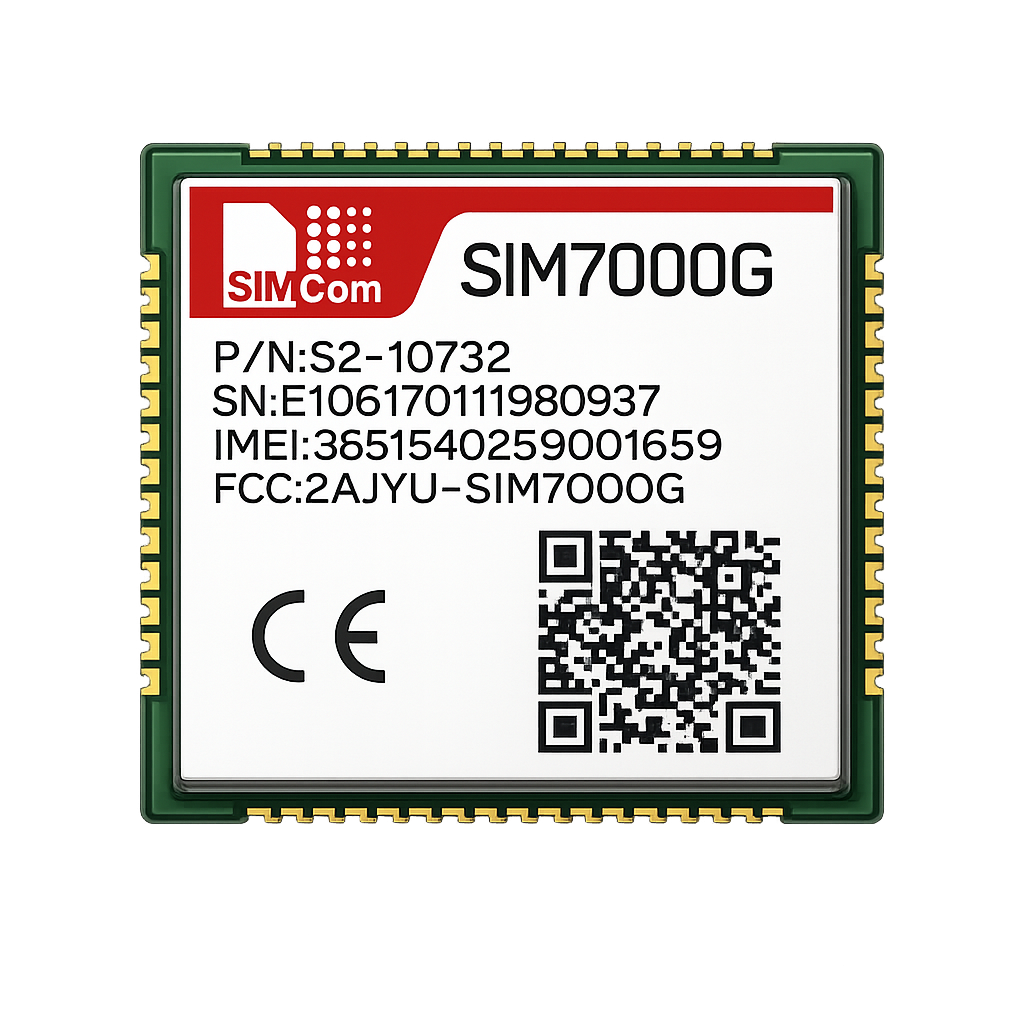
Images/SIM7000G.png
